VughtseProgrammeerclub/tekenmachine_2026/fotos/PXL_20260317_203404150.jpg

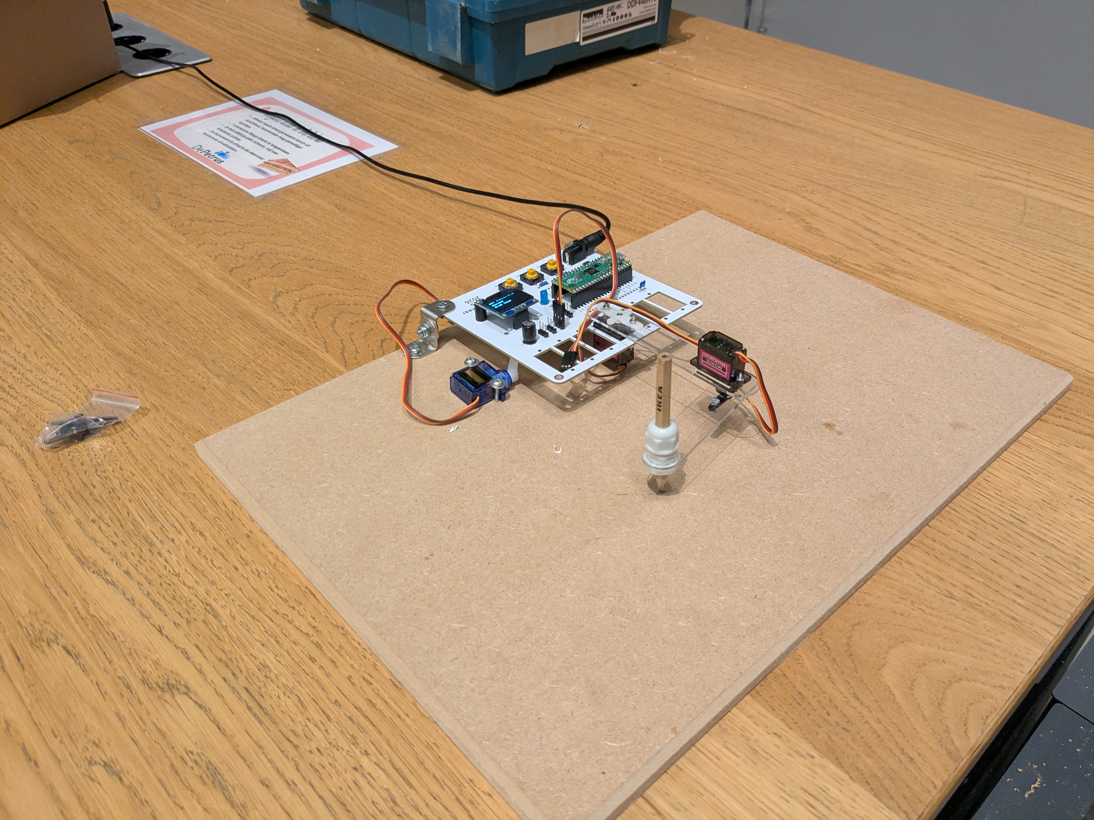
fotos/PXL_20260317_203404150.jpg
