VughtseProgrammeerclub/tekenmachine_2026/fotos/PXL_20260317_203412434.jpg

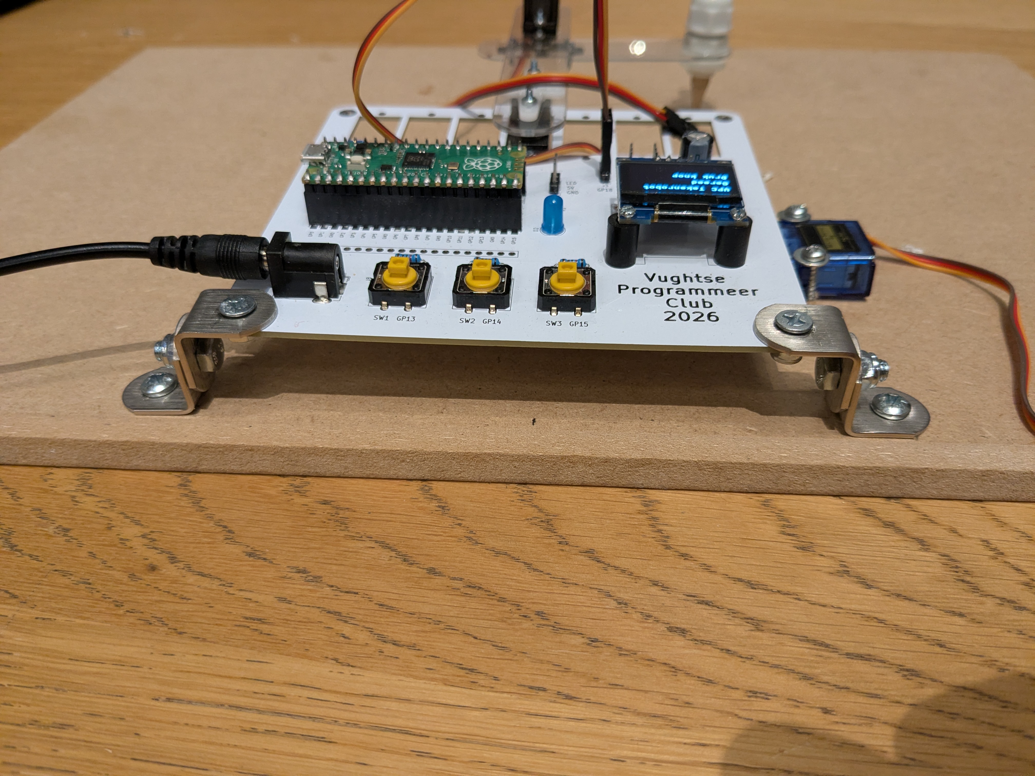
fotos/PXL_20260317_203412434.jpg
