VughtseProgrammeerclub/tekenmachine_2026/fotos/PXL_20260317_203420933.jpg

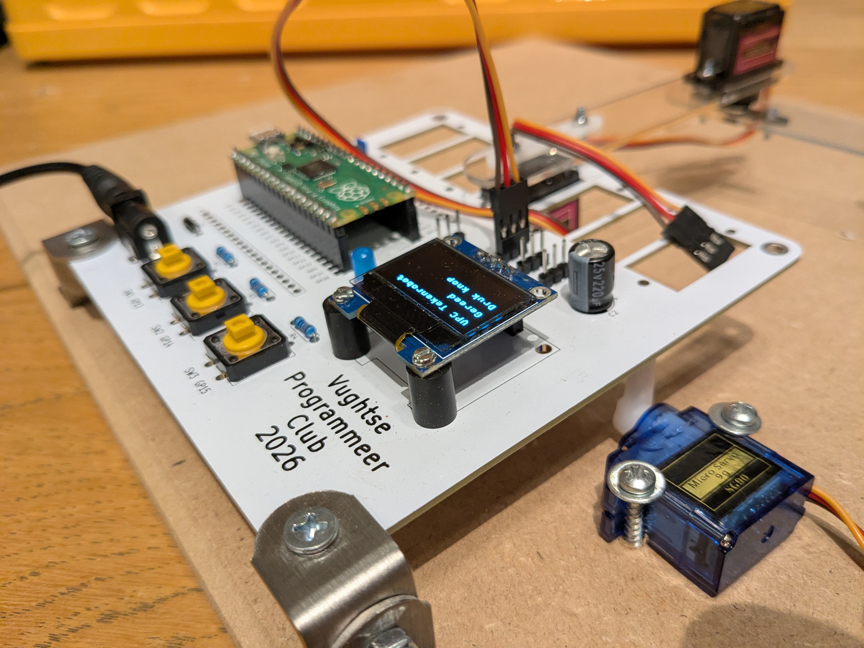
fotos/PXL_20260317_203420933.jpg
