VughtseProgrammeerclub/tekenmachine_2026/fotos/PXL_20260317_203424862.jpg

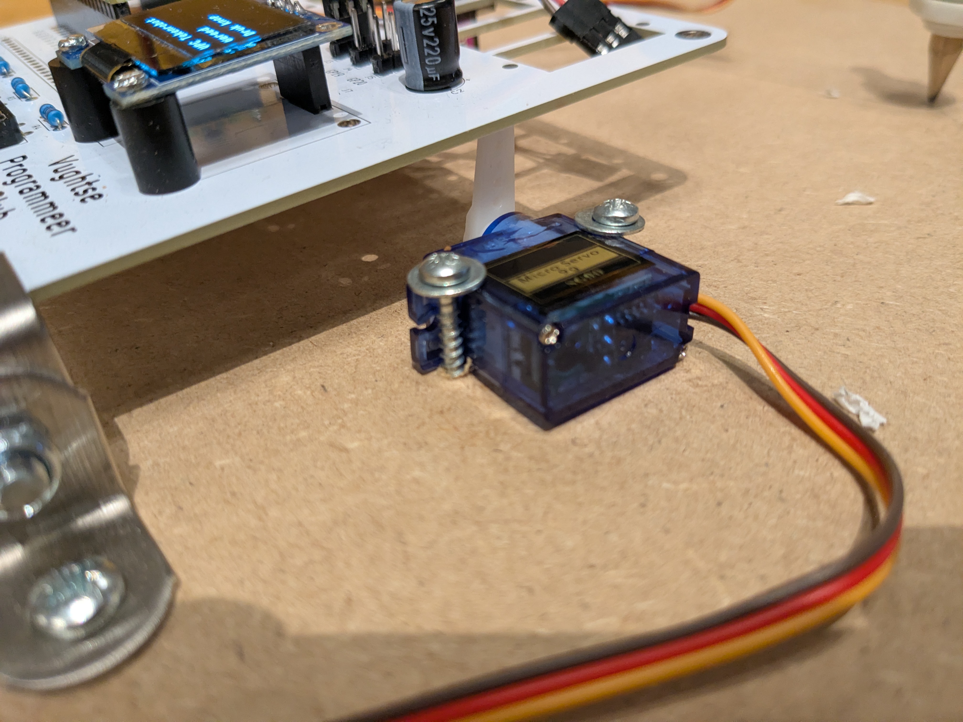
fotos/PXL_20260317_203424862.jpg
