VughtseProgrammeerclub/tekenmachine_2026/fotos/PXL_20260317_203439882.jpg

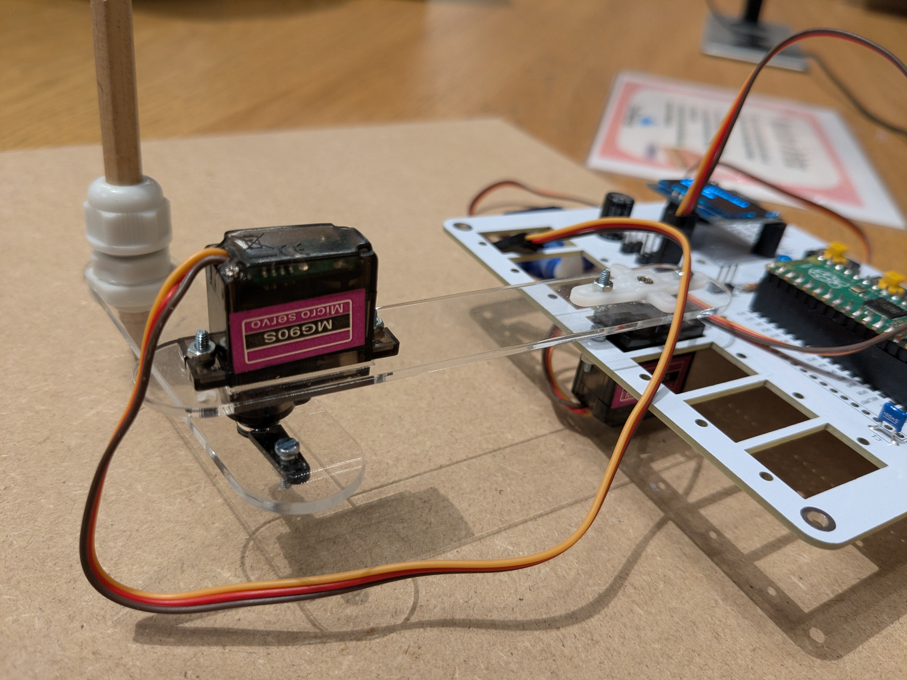
fotos/PXL_20260317_203439882.jpg
