VughtseProgrammeerclub/tekenmachine_2026/fotos/PXL_20260317_203451094.jpg

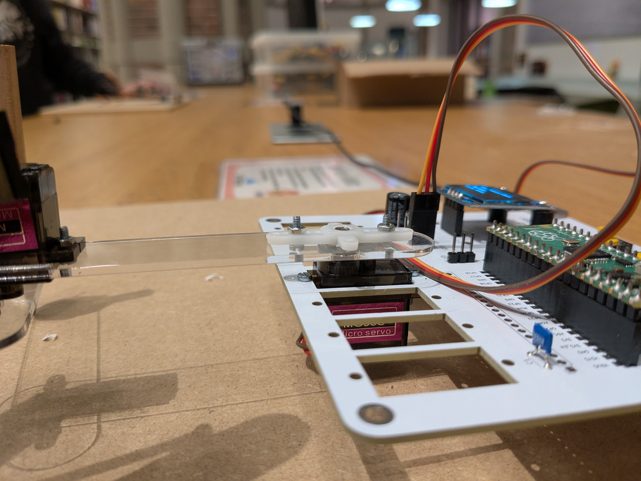
fotos/PXL_20260317_203451094.jpg
