VughtseProgrammeerclub/tekenmachine_2026/fotos/PXL_20260317_203503703.jpg

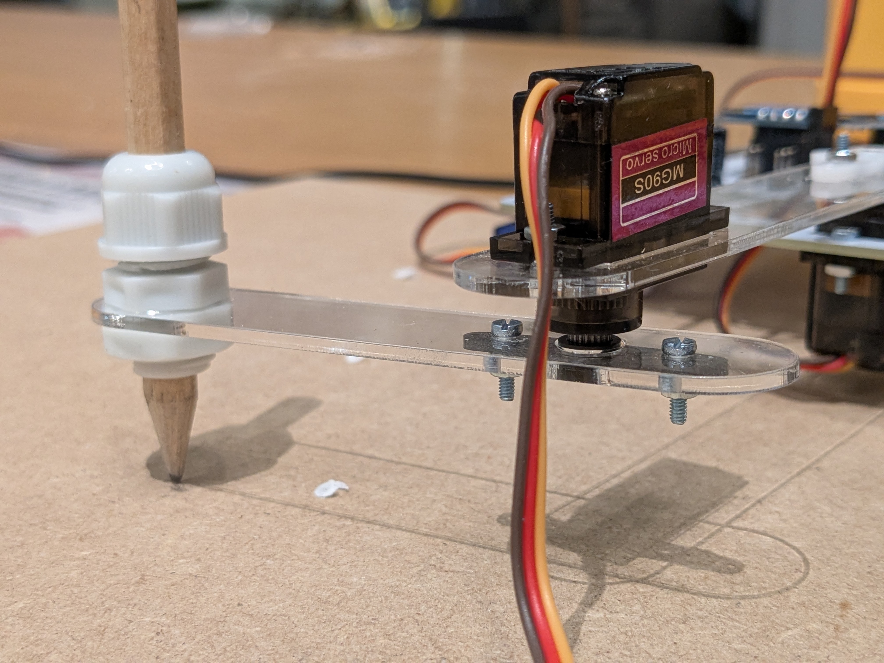
fotos/PXL_20260317_203503703.jpg
