VughtseProgrammeerclub/tekenmachine_2026/fotos/PXL_20260317_203514550.jpg

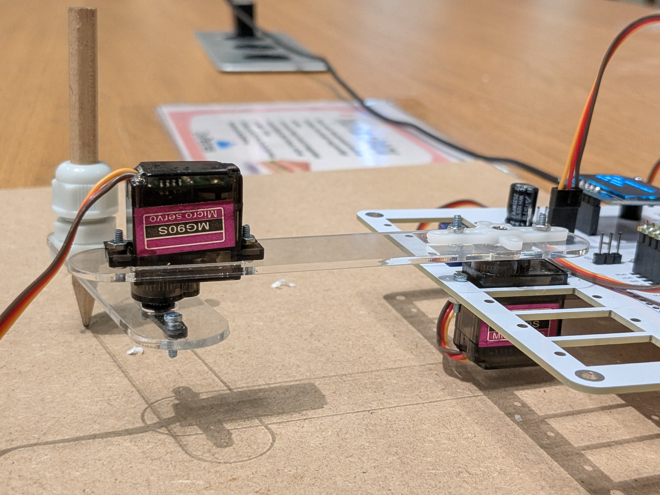
fotos/PXL_20260317_203514550.jpg
