VughtseProgrammeerclub/tekenmachine_2026/goniometrie/vpc - tekenmachine - goniometrie 2026-03-31_1555_cd.jpg

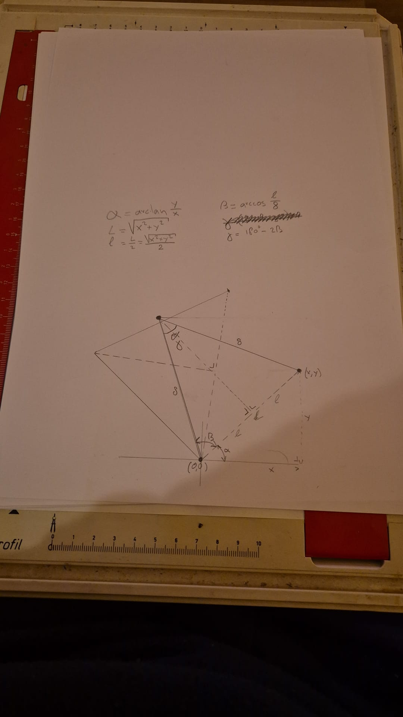
goniometrie/vpc - tekenmachine - goniometrie 2026-03-31_1555_cd.jpg
